JonasVgt/sextant/FreeCAD/Viewscope-CollarTop.3mf

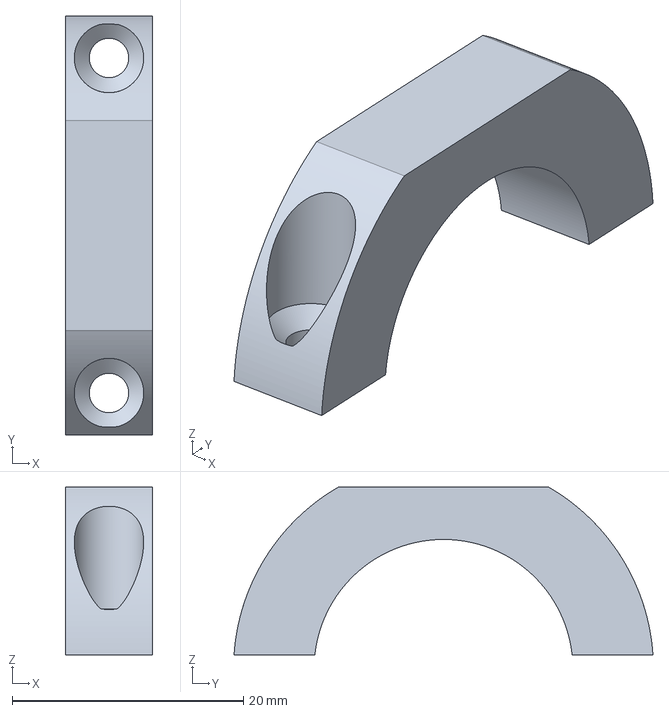
[picture p16: CAD file, 2024-06-07]
FreeCAD/Viewscope-CollarTop.3mf
7.50 x 36.3 x 14.5 mm
