JonasVgt/sextant/FreeCAD/Viewscope-CollarBottom.3mf

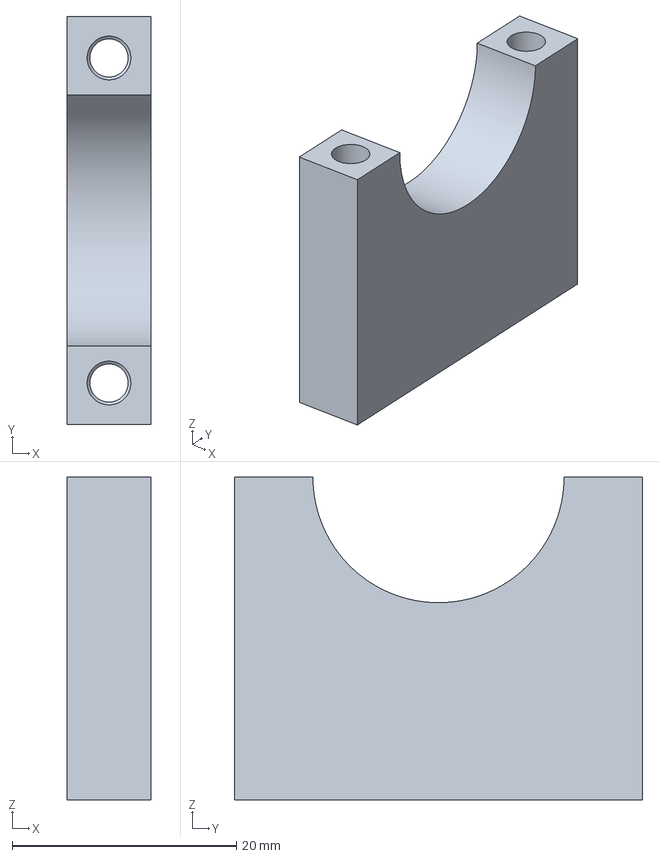
[picture p17: CAD file, 2024-06-06]
FreeCAD/Viewscope-CollarBottom.3mf
7.50 x 36.4 x 28.8 mm
