JonasVgt/sextant/FreeCAD/Handle_CollarTop.3mf

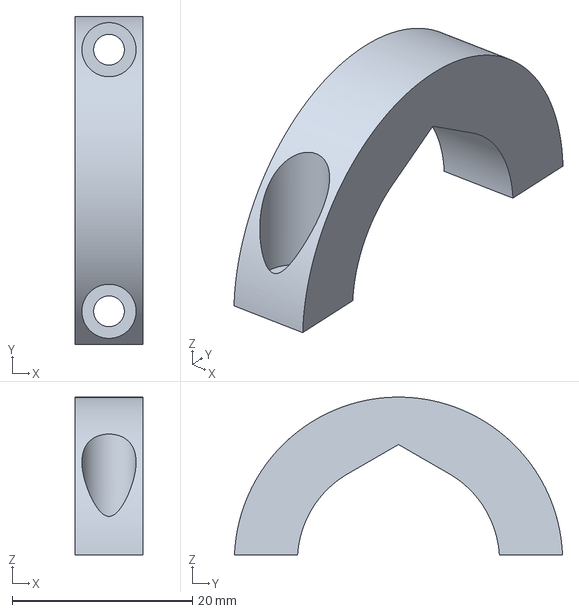
[picture p18: CAD file, 2024-06-05]
FreeCAD/Handle_CollarTop.3mf
7.50 x 36.4 x 17.5 mm
